CoderTobi/Teufel-Concept-E300-reverse-engineering/Analyse/Paket Analyse Bass.png

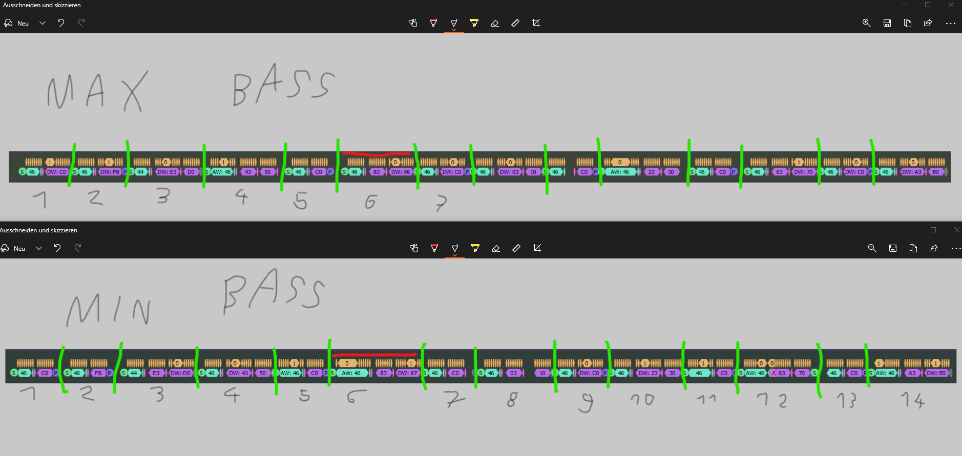
Analyse/Paket Analyse Bass.png
