CoderTobi/Teufel-Concept-E300-reverse-engineering/Bilder/20230907_212019.jpg

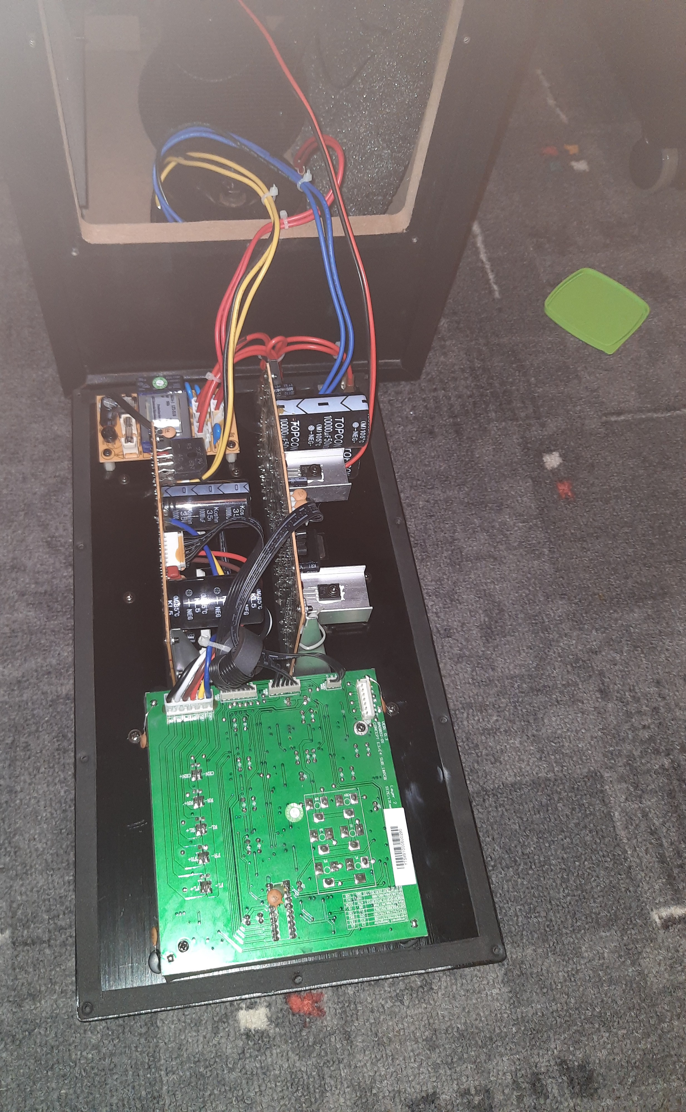
Bilder/20230907_212019.jpg
