CoderTobi/Teufel-Concept-E300-reverse-engineering/Bilder/20240312_225326.jpg

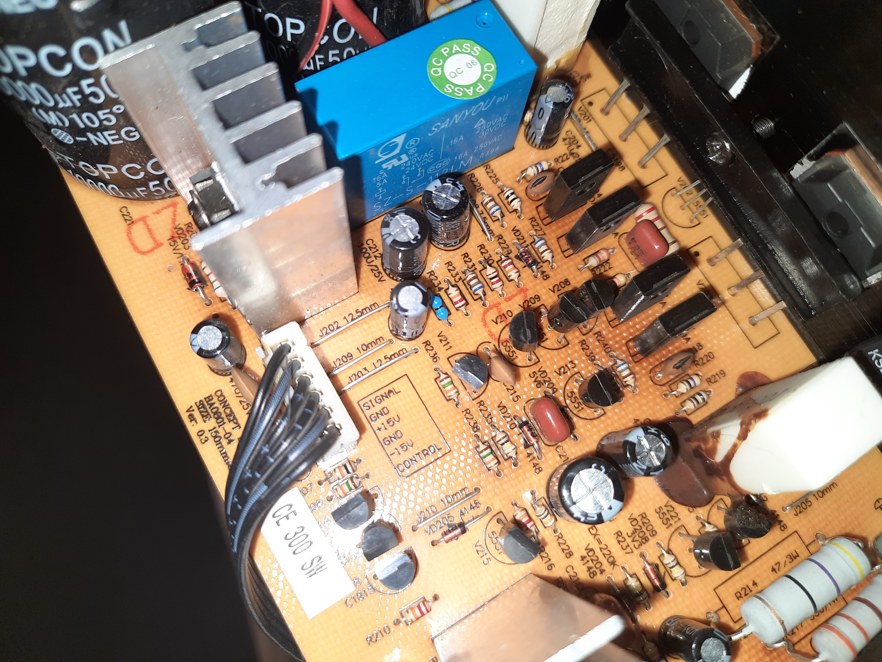
Bilder/20240312_225326.jpg
