CoderTobi/Teufel-Concept-E300-reverse-engineering/Bilder/IMG-20230907-WA0005.jpeg

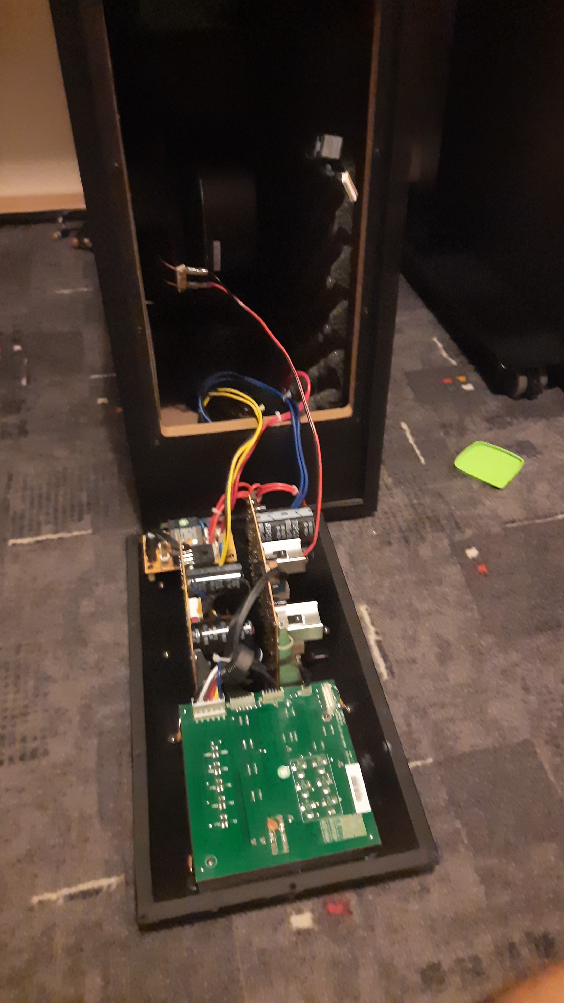
Bilder/IMG-20230907-WA0005.jpeg
