CoderTobi/Teufel-Concept-E300-reverse-engineering/Fritzing/Perfboard-flipped.png

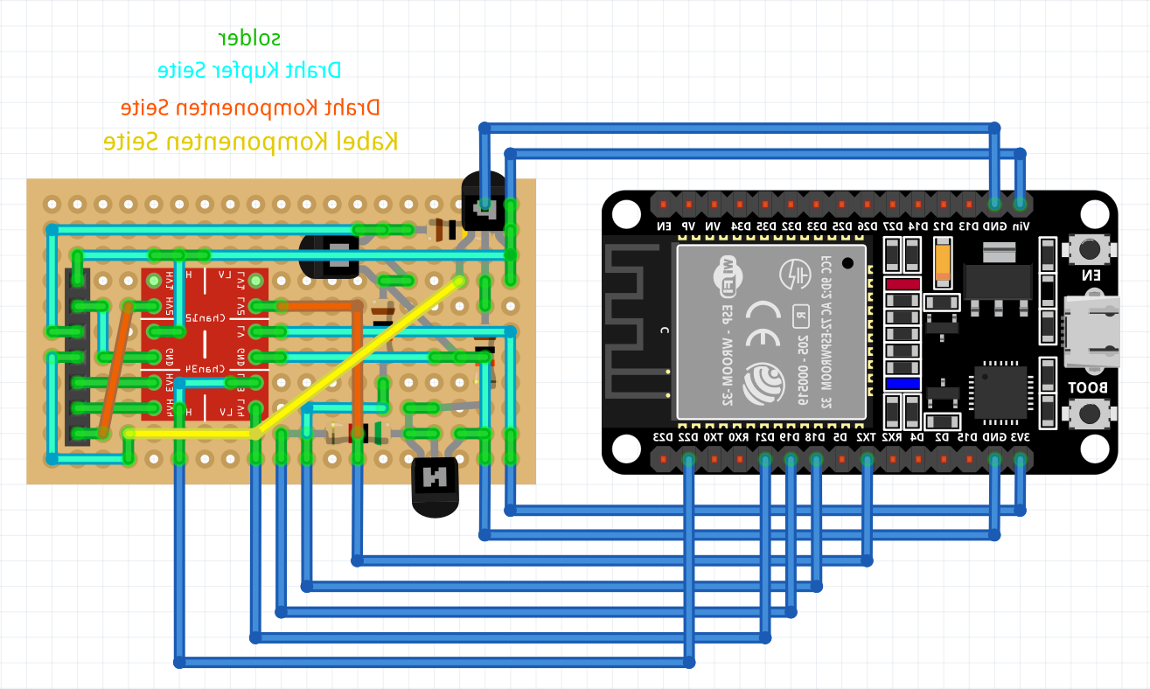
Fritzing/Perfboard-flipped.png
