CoderTobi/Teufel-Concept-E300-reverse-engineering/Fritzing/Schaltplan.png

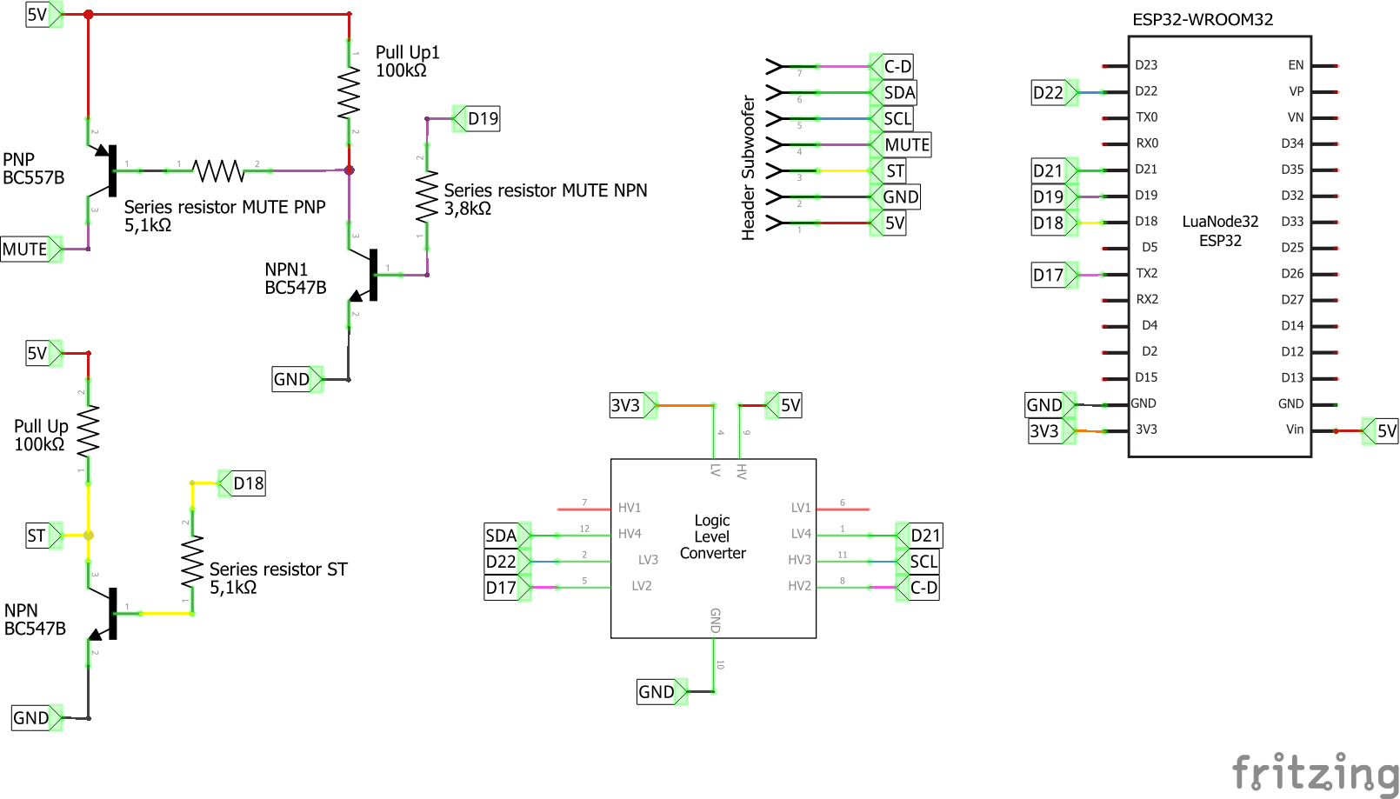
Fritzing/Schaltplan.png
