CoderTobi/Teufel-Concept-E300-reverse-engineering/LT Spice/Standby Relais.asc

Amps: LED
D2: diode
Q1: npn; 2N5551
Q2: pnp; 2N5401
R1: res; 200
R2: res; 10k
R3: res; 47k
R4: res; 10k
Relais_Amp: sw
V1: voltage; 1V
V2: voltage; 5
Named nets: 0
