CoderTobi/Teufel-Concept-E300-reverse-engineering/KiCad/SatelliteAMP/SatelliteAMP/SatelliteAMP.kicad_sch

## KiCad design KiCad/SatelliteAMP/SatelliteAMP/SatelliteAMP.kicad_sch (2025-09-12)

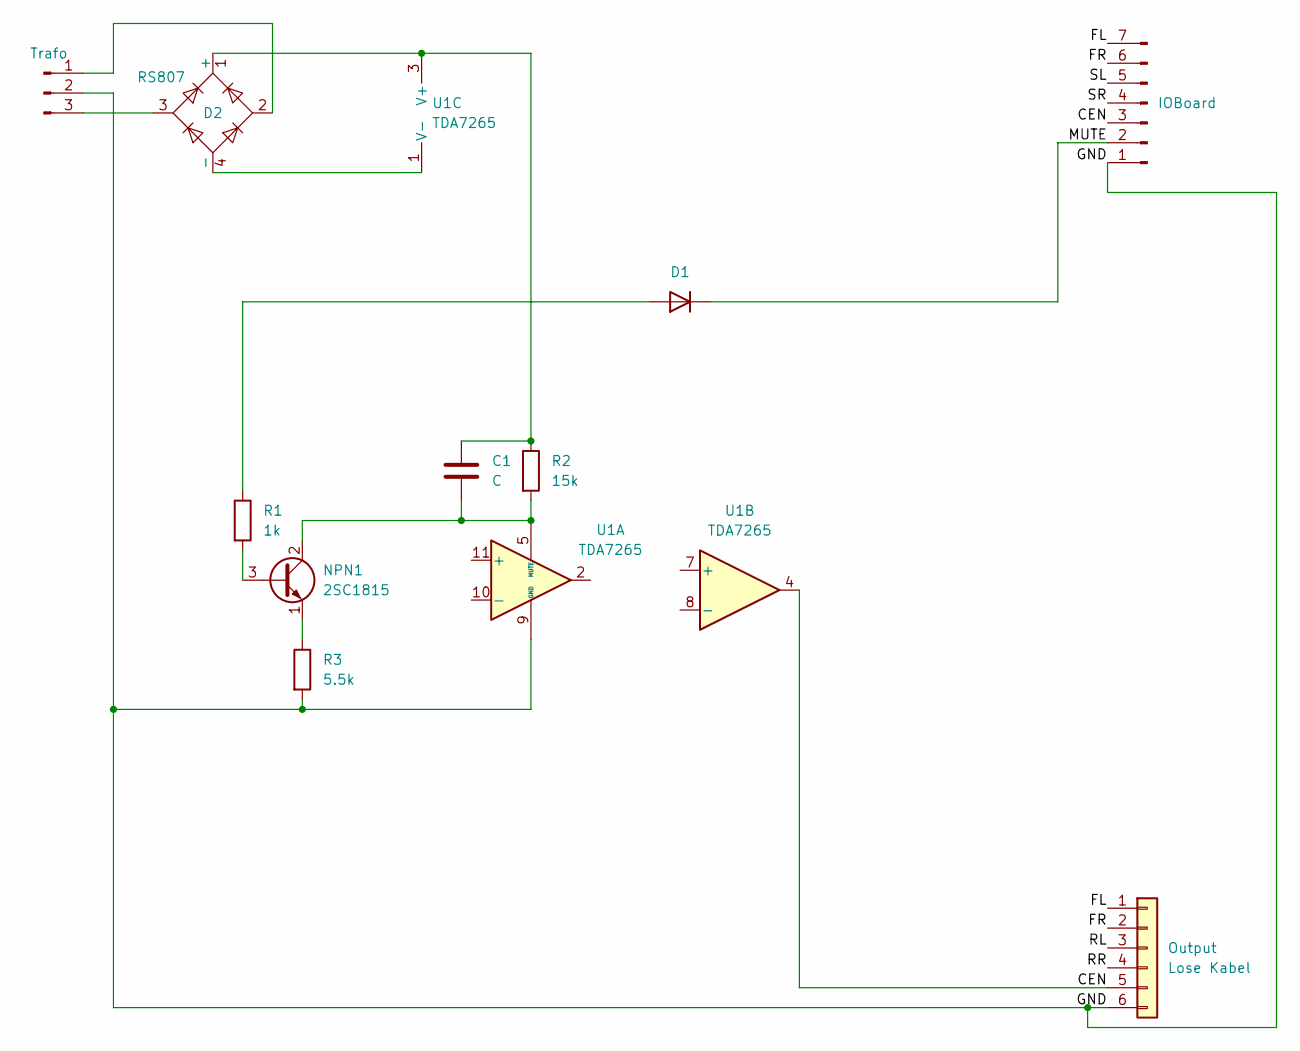
[picture p27: schematic SatelliteAMP.kicad_sch]

Parts:
C1: C
D1: D
D2: RS807; Diode_Bridge_Vishay_GBU
IOBoard: Conn_01x07_Pin
NPN1: 2SC1815; TO-92_Inline
Output: Lose Kabel
R1: 1k
R2: 15k
R3: 5.5k
Trafo: Conn_01x03_Pin
U1: TDA7265; TO-220-11_P3.4x5.08mm_StaggerOdd_Lead4.85mm_Vertical

Connections:
CEN: IOBoard.3, Output.5, U1.4
FL: IOBoard.7, Output.1
FR: IOBoard.6, Output.2
GND: IOBoard.1, Output.6, R3.2, Trafo.2, U1.9 (GND)
MUTE: D1.1 (K), IOBoard.2
unnamed: C1.1, D2.1 (+), R2.1, U1.3 (V+)
unnamed: C1.2, NPN1.2 (C), R2.2, U1.5 (MUTE)
unnamed: D1.2 (A), R1.1
unnamed: D2.2, Trafo.1
unnamed: D2.3, Trafo.3
unnamed: D2.4 (-), U1.1 (V-), U1.6 (V-)
unnamed: NPN1.1 (E), R3.1
unnamed: NPN1.3 (B), R1.2
RL: Output.3
RR: Output.4
SL: IOBoard.5
SR: IOBoard.4
