CoderTobi/Teufel-Concept-E300-reverse-engineering/Bilder/20240312_182101.jpg

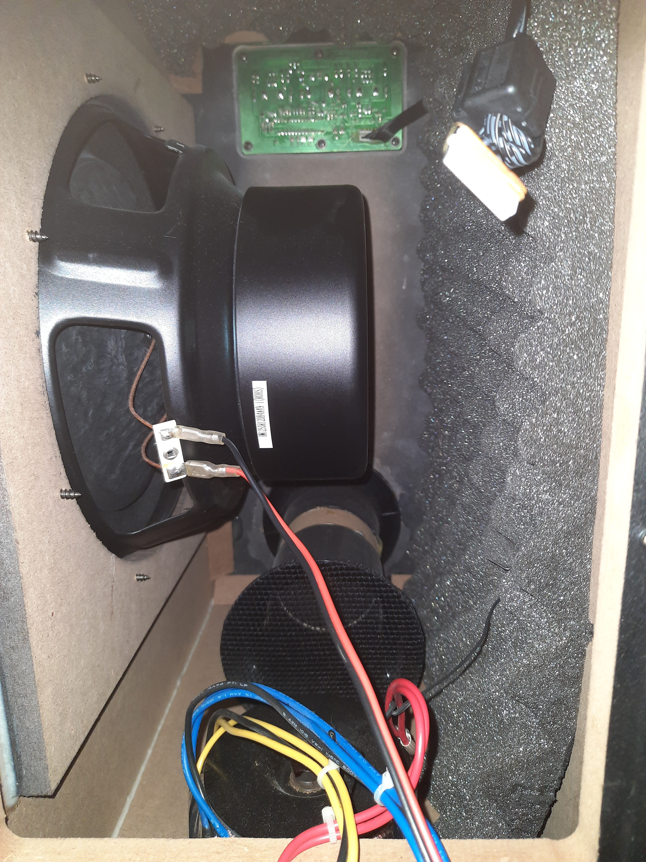
Bilder/20240312_182101.jpg
