CoderTobi/Teufel-Concept-E300-reverse-engineering/Bilder/20240312_182449.jpg

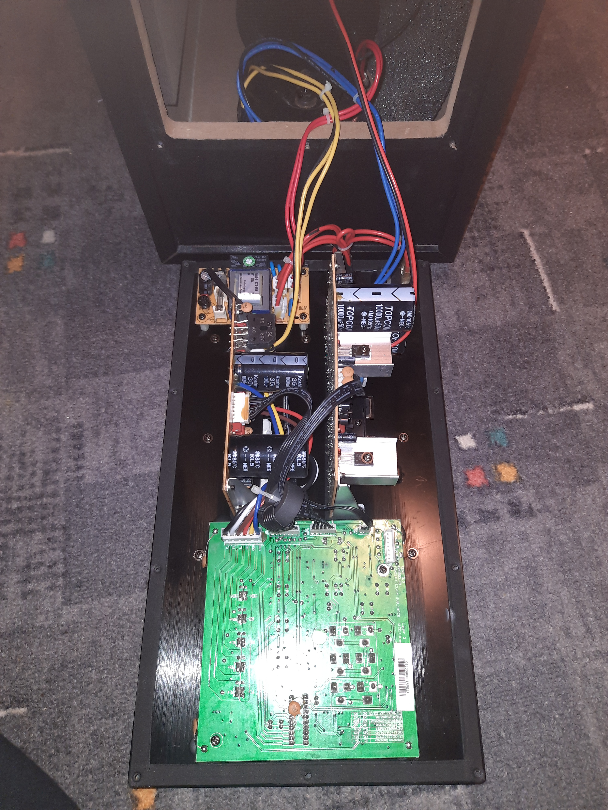
Bilder/20240312_182449.jpg
