CoderTobi/Teufel-Concept-E300-reverse-engineering/Bilder/20240312_200321.jpg

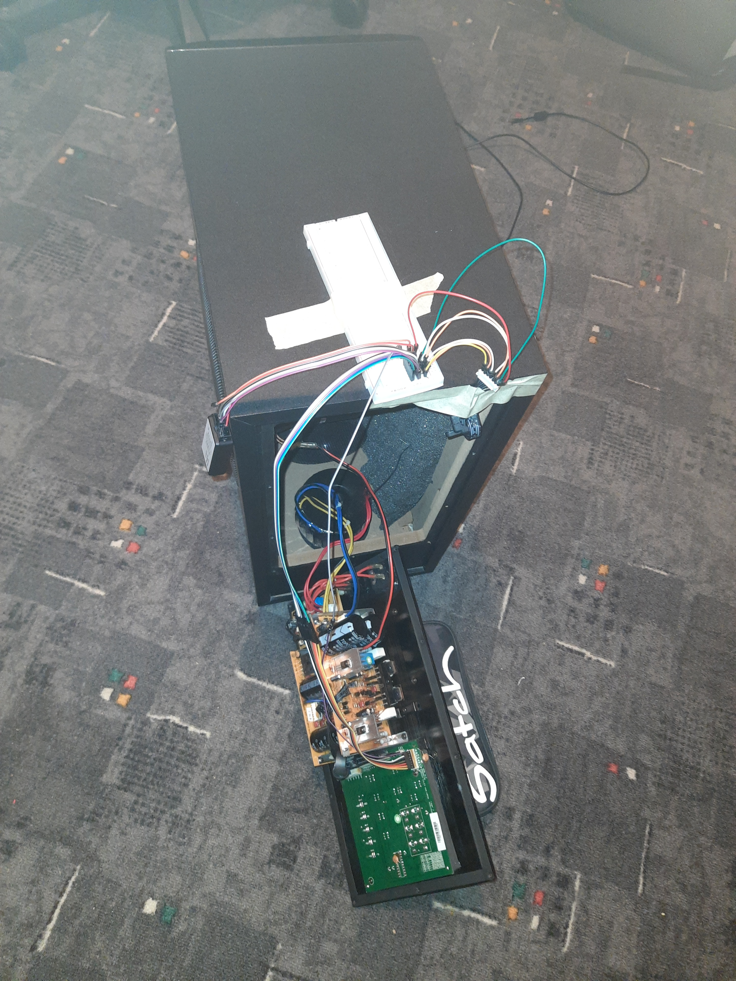
Bilder/20240312_200321.jpg
