CoderTobi/Teufel-Concept-E300-reverse-engineering/Bilder/20240312_200334.jpg

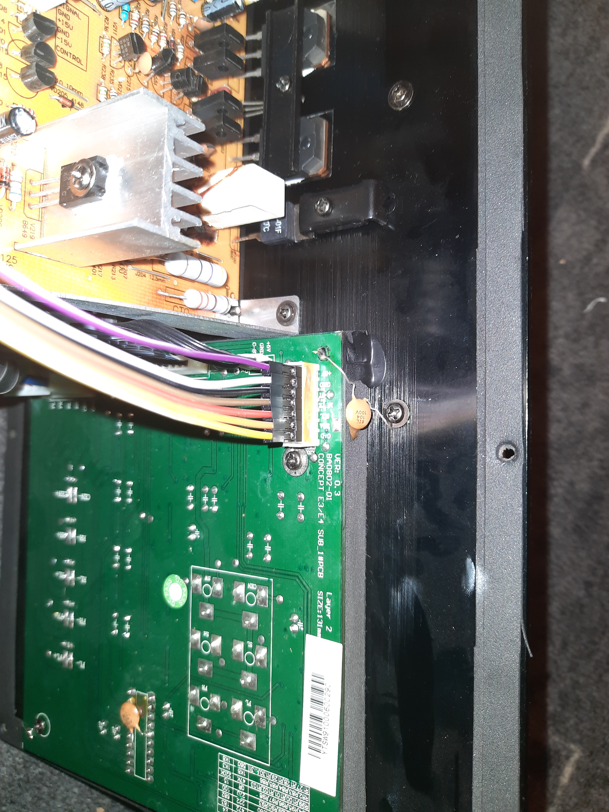
Bilder/20240312_200334.jpg
