CoderTobi/Teufel-Concept-E300-reverse-engineering/Bilder/20240312_225204.jpg

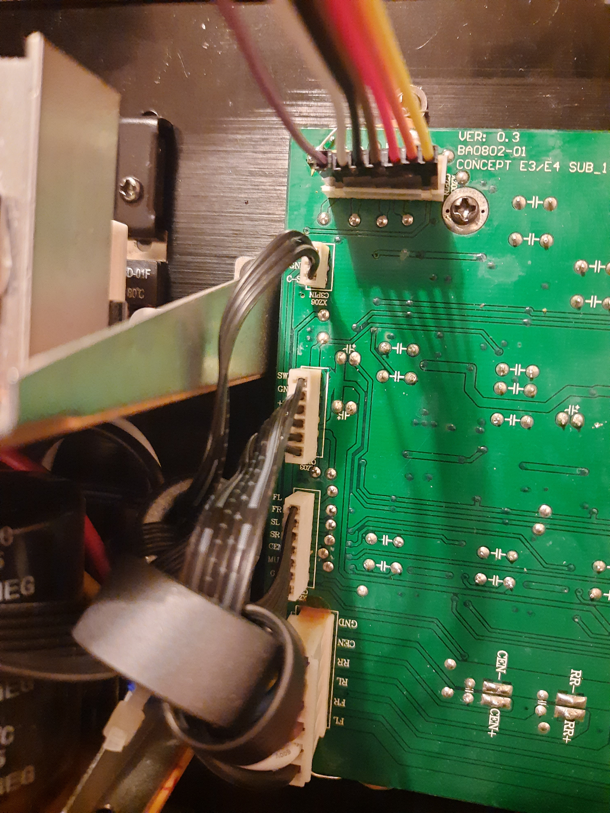
Bilder/20240312_225204.jpg
